milar111/LYME/simulations/receiver.asc

C1: cap; 8.2p
C3: polcap; 100µF
C4: cap; 25p
I1: current; ""; AC 1
R1: res; 2.2k
R2: res; 75
U1: UniversalOpAmp
V1: voltage; 9
V2: voltage; 9
Named nets: 0
.ac dec 100 10 100Meg
