milar111/LYME/simulations/transmitter.asc

C1: polcap; 47µ
C2: cap; 100n
D1: LED
Q1: npn; 2N2222
R1: res; 1k
R2: res; 5k
R3: res; 5k
R4: res; 100
V1: voltage; 5
V2: voltage; SINE(0.5 0.5 5Meg)
Named nets: 0
.tran 10u
